DansDesigns/ComBadge/Case/Screenshot 2025-02-11 154952.png

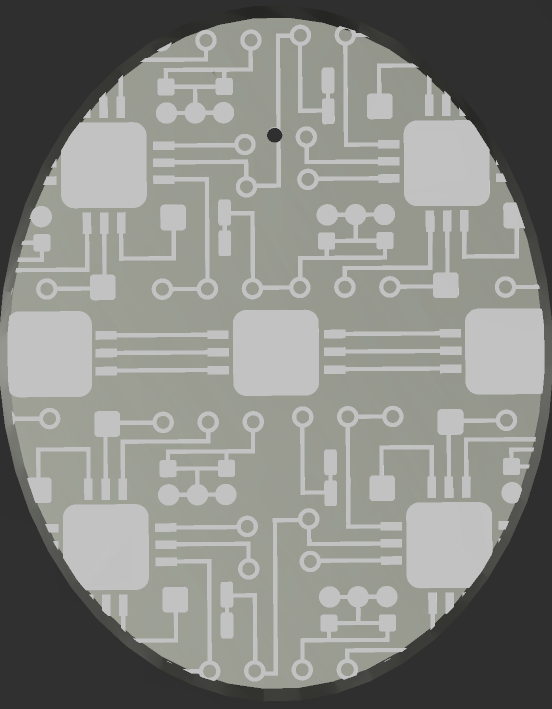
Case/Screenshot 2025-02-11 154952.png
