DansDesigns/ComBadge/Case/Screenshot 2025-02-11 155020.png

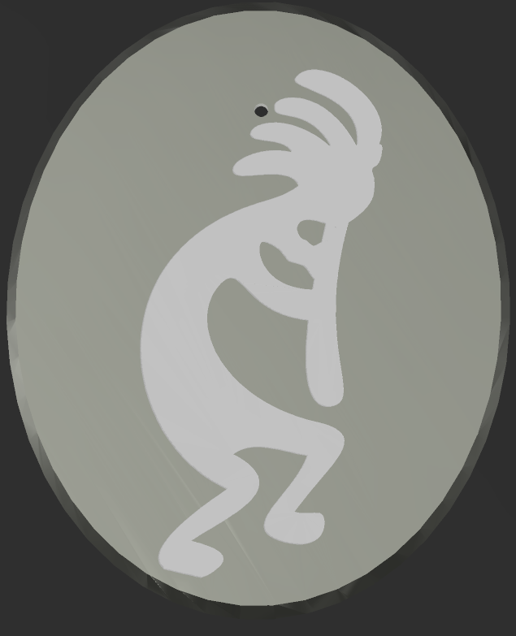
Case/Screenshot 2025-02-11 155020.png
