DansDesigns/ComBadge/Case/Screenshot 2025-02-11 155047.png

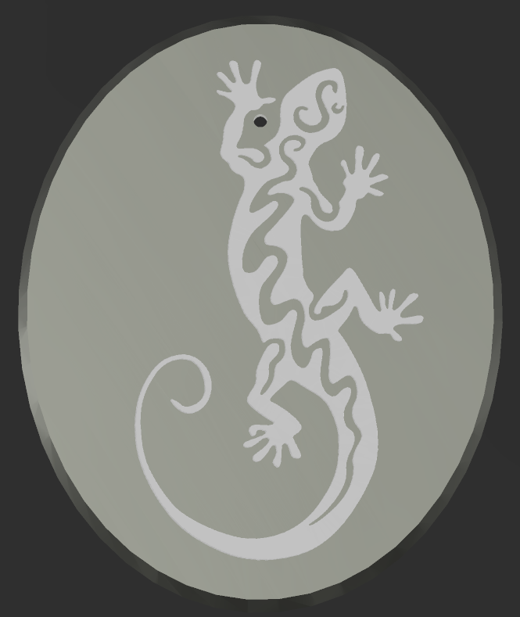
Case/Screenshot 2025-02-11 155047.png
