DansDesigns/ComBadge/Case/Screenshot 2025-02-11 155144.png

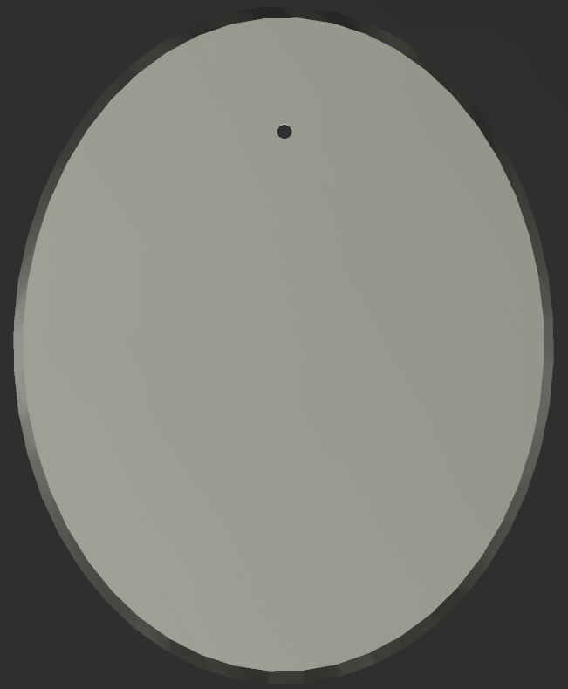
Case/Screenshot 2025-02-11 155144.png
