DansDesigns/ComBadge/Case/Screenshot 2025-02-14 155029.png

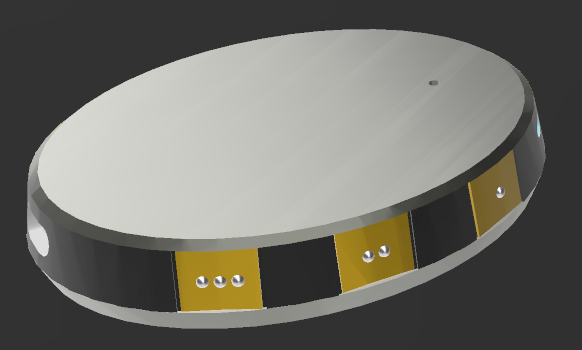
Case/Screenshot 2025-02-14 155029.png
