DansDesigns/ComBadge/Case/Screenshot 2025-02-14 155050.png

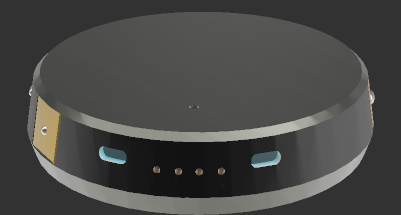
Case/Screenshot 2025-02-14 155050.png
