DansDesigns/ComBadge/Case/Screenshot 2025-02-14 160312.png

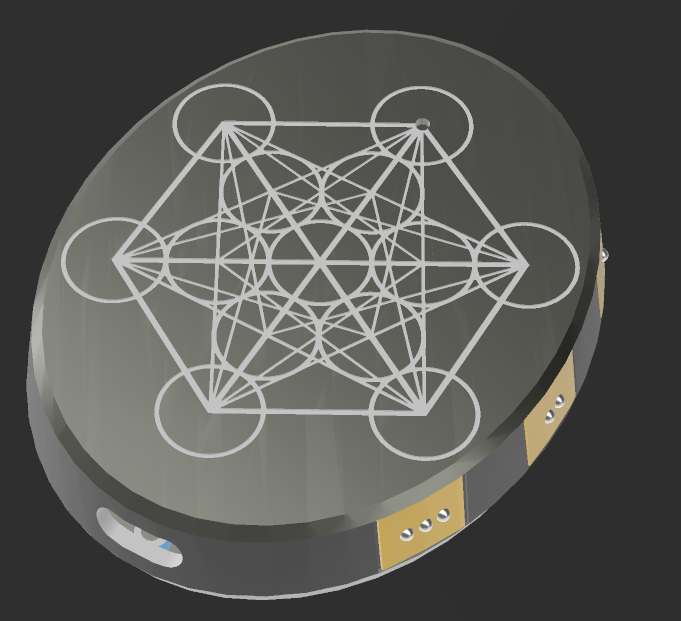
Case/Screenshot 2025-02-14 160312.png
