DansDesigns/ComBadge/Case/Screenshot 2025-02-14 160329.png

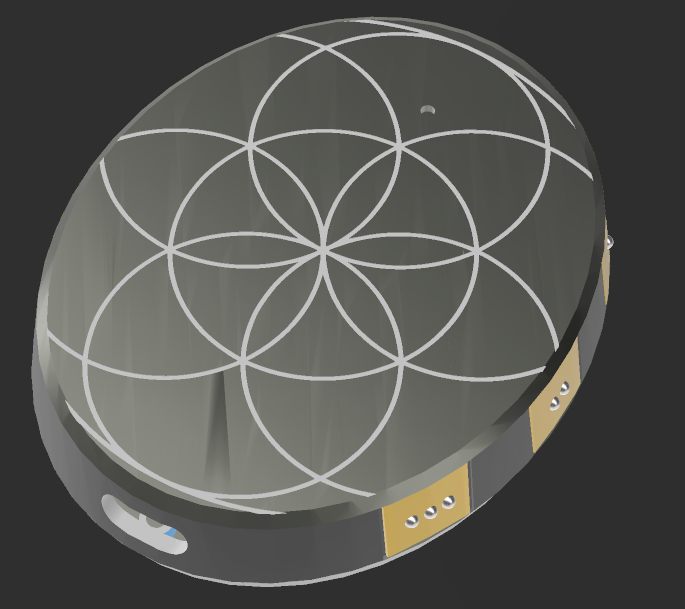
Case/Screenshot 2025-02-14 160329.png
