DansDesigns/ComBadge/Case/Screenshot 2025-02-14 160347.png

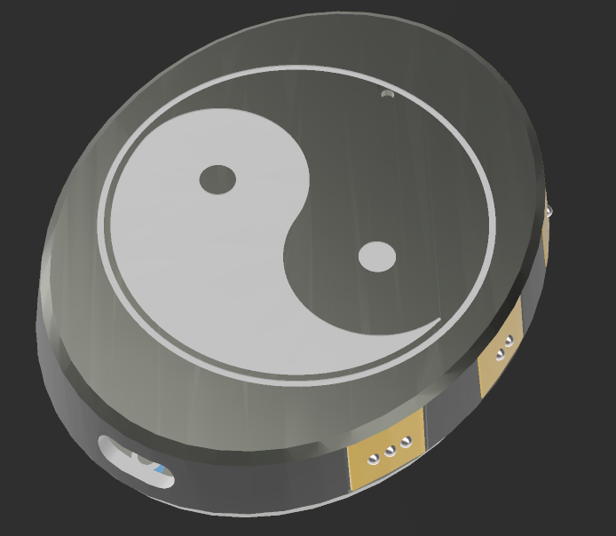
Case/Screenshot 2025-02-14 160347.png
