DansDesigns/ComBadge/Data_Sheets/mpu6050_1.png

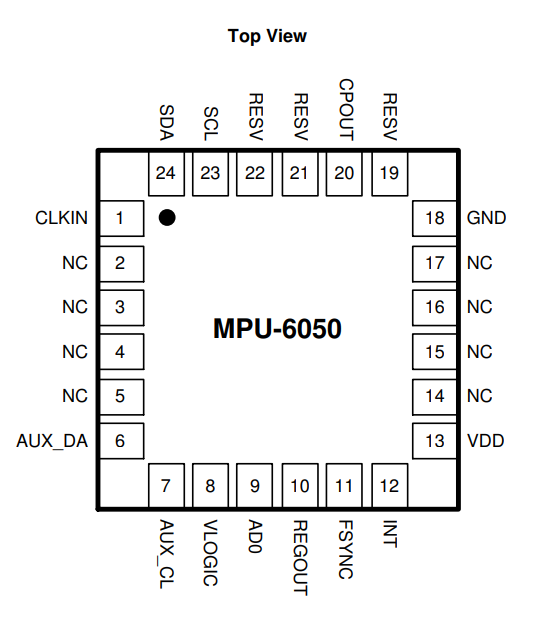
Data_Sheets/mpu6050_1.png
