DansDesigns/ComBadge/Data_Sheets/mpu6050_2.png

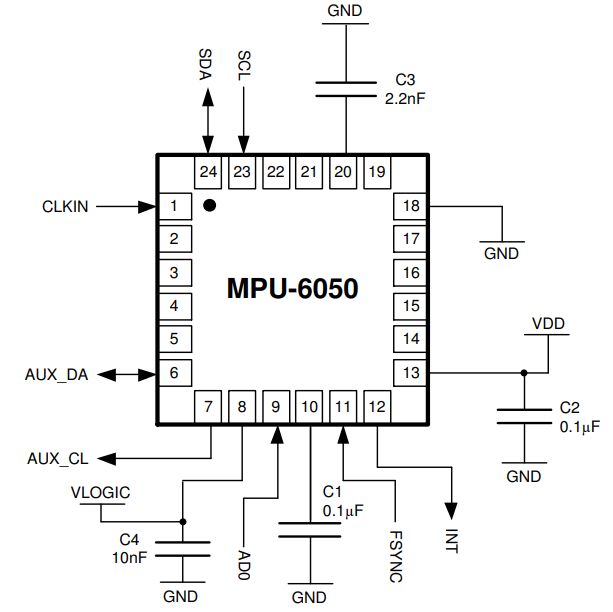
Data_Sheets/mpu6050_2.png
