DansDesigns/ComBadge/Data_Sheets/mpu6050_3.png

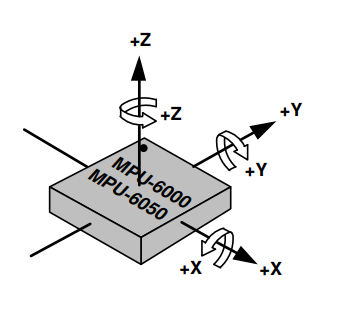
Data_Sheets/mpu6050_3.png
