DansDesigns/ComBadge/Data_Sheets/MSTG-SG21.png

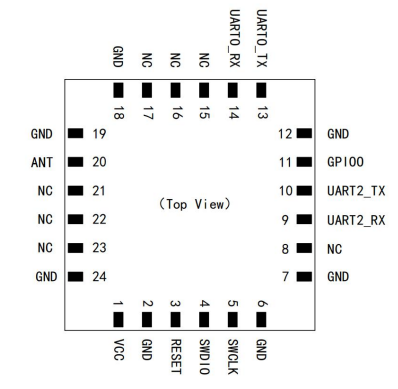
Data_Sheets/MSTG-SG21.png
