DansDesigns/ComBadge/Data_Sheets/MTCH6012.png

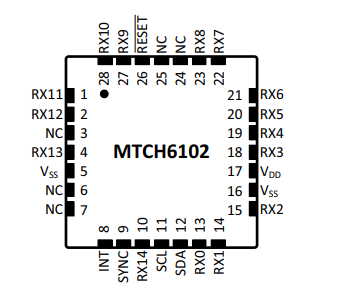
Data_Sheets/MTCH6012.png
