DansDesigns/ComBadge/Data_Sheets/ZiFiSense-MSTG-ST10.png

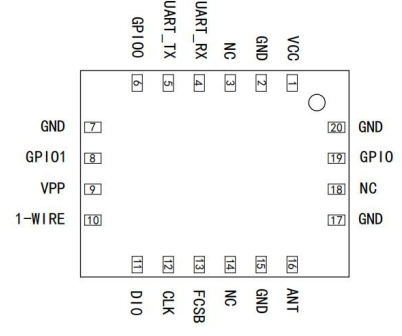
Data_Sheets/ZiFiSense-MSTG-ST10.png
