DansDesigns/ComBadge/Pictures/waveguide_1.png

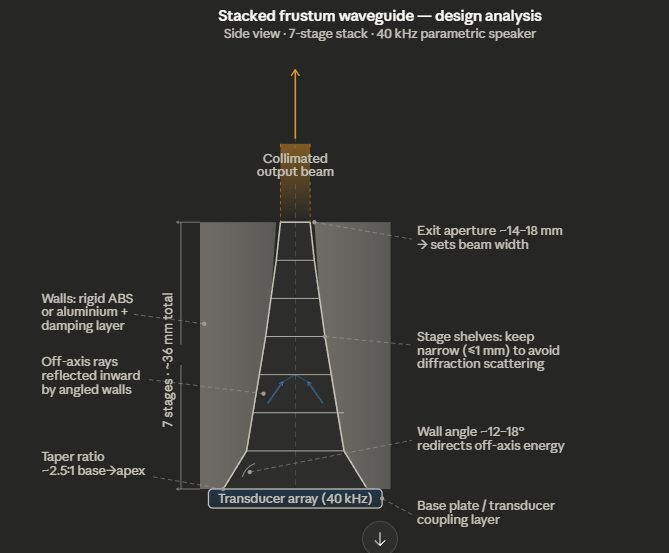
Pictures/waveguide_1.png
